Sahan-Siri/Smart-Nest/3D Model/01.jpg

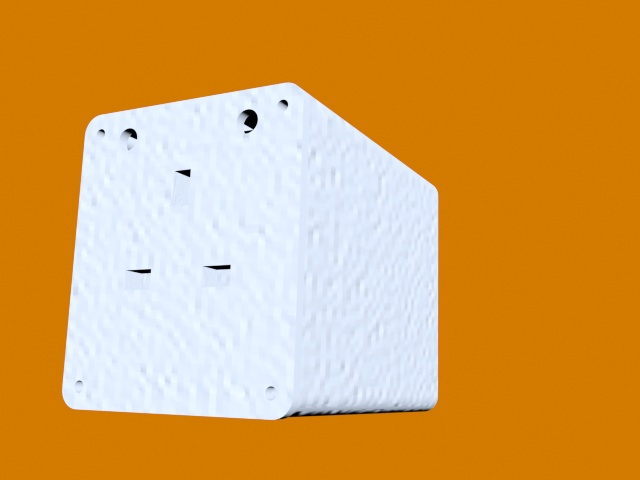
3D Model/01.jpg
