Sahan-Siri/Smart-Nest/3D Model/02.jpg

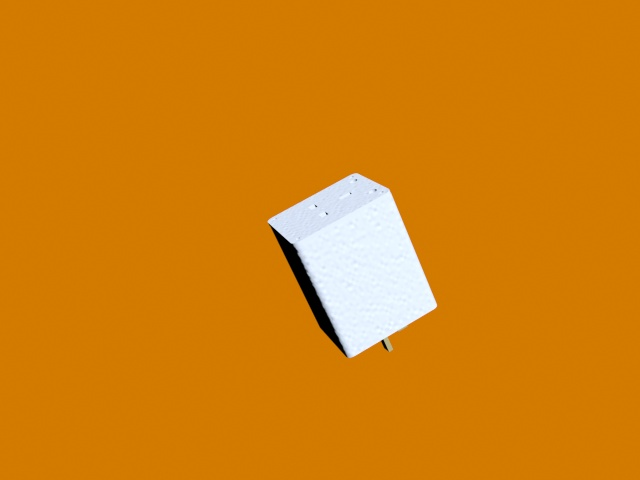
3D Model/02.jpg
